htl-leo-club-embedded-iot/GoalFinder/docs/images/fotodoc_assemby/orig/PXL_20251103_104743675.jpg

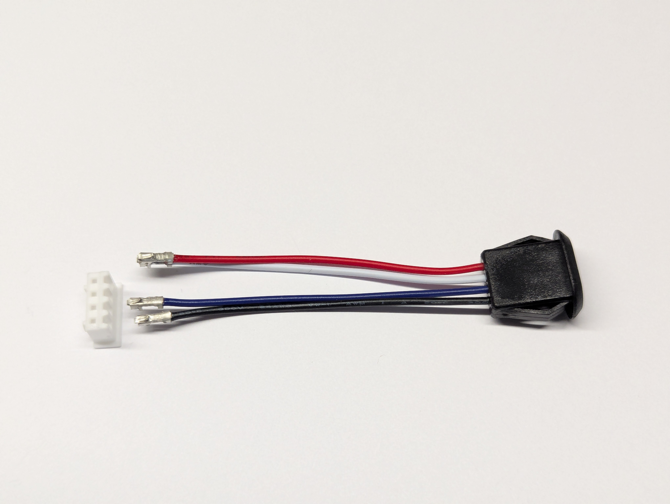
docs/images/fotodoc_assemby/orig/PXL_20251103_104743675.jpg
