htl-leo-club-embedded-iot/GoalFinder/docs/images/fotodoc_assemby/orig/PXL_20251103_160812800.jpg

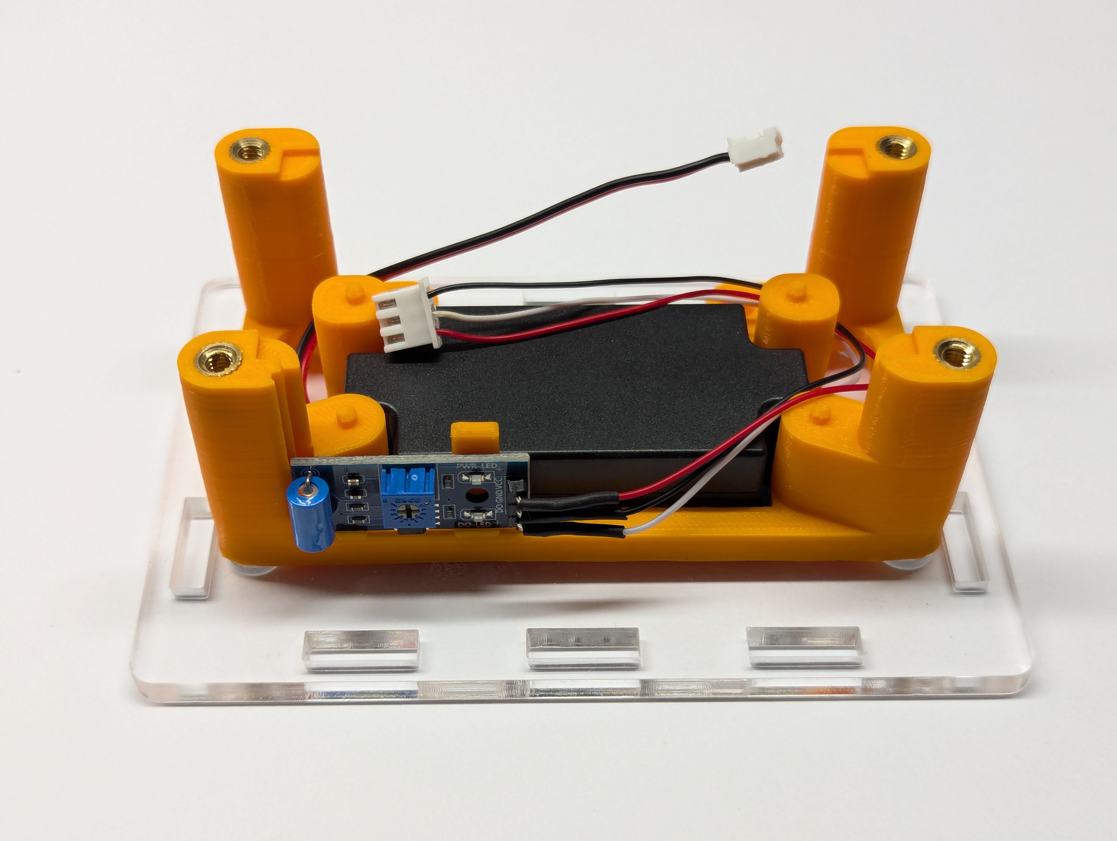
docs/images/fotodoc_assemby/orig/PXL_20251103_160812800.jpg
