htl-leo-club-embedded-iot/GoalFinder/docs/images/fotodoc_assemby/orig/PXL_20251103_201643062.jpg

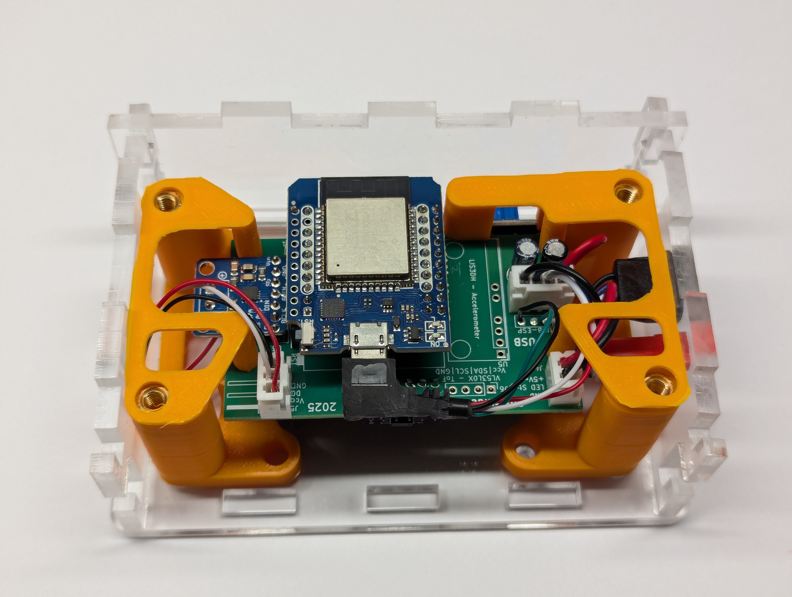
docs/images/fotodoc_assemby/orig/PXL_20251103_201643062.jpg
