htl-leo-club-embedded-iot/GoalFinder/docs/images/fotodoc_assemby/orig/PXL_20251103_222439220.jpg

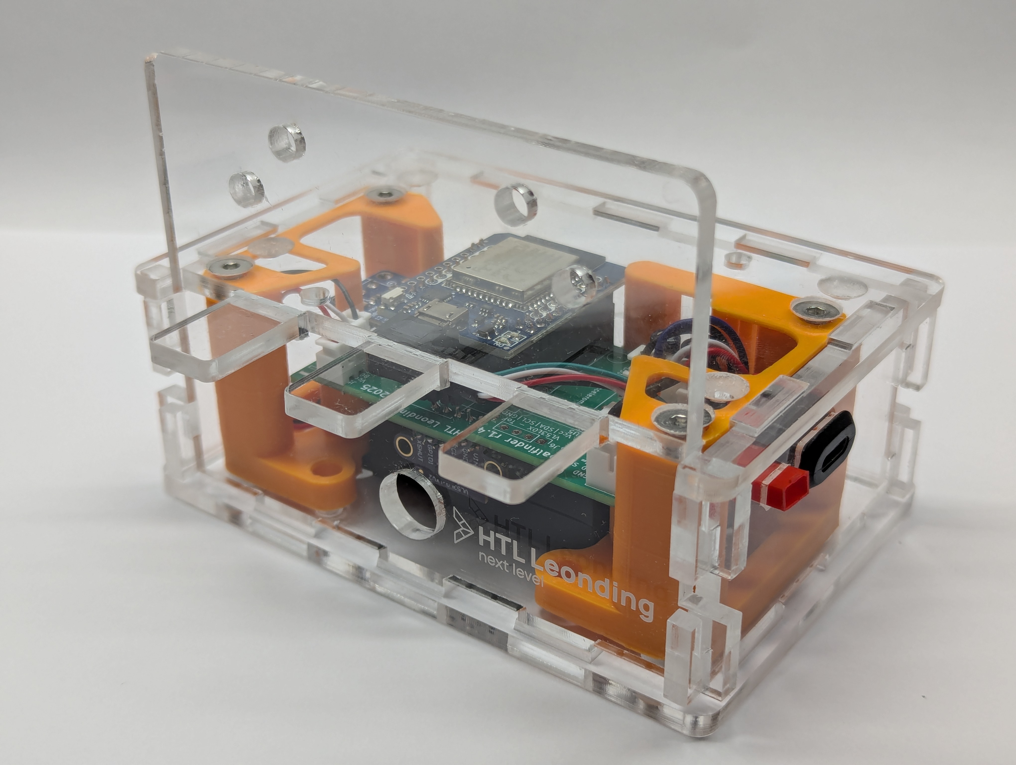
docs/images/fotodoc_assemby/orig/PXL_20251103_222439220.jpg
