htl-leo-club-embedded-iot/GoalFinder/embedded/src/util/Logger.h

/* ===============================================================================
 * (c) HTBLA Leonding 2024 - 2026
 * - - - - - - - - - - - - - - - - - - - - - - - - - - - - - - - - - - - - - - - -
 * Licensed under MIT License.
 *
 * Unless required by applicable law or agreed to in writing, software
 * distributed under the License is distributed on an "AS IS" BASIS,
 * WITHOUT WARRANTIES OR CONDITIONS OF ANY KIND, either express or implied.
 * See the License for the specific language governing permissions and
 * limitations under the license.
 * - - - - - - - - - - - - - - - - - - - - - - - - - - - - - - - - - - - - - - - -
 * All trademarks used in this document are property of their respective owners.
 * =============================================================================== */

#ifndef ___LOGGER_H
#define ___LOGGER_H

#include <WString.h>
#include "freertos/FreeRTOS.h"
#include "freertos/queue.h"
#include <Arduino.h>
#include "../Settings.h"

class Logger
{
public:
    enum class LogLevel
    {
        OK,
        DEBUG,
        INFO,
        WARN,
        ERROR
    };

    struct LogEntry {
        String message;
        String file;
        LogLevel level;
    };

    static void Begin(unsigned long baudRate = 115200);

    static void Log(const String &message);
    static void Log(const String &message, LogLevel level);
    static void Log(const String &message, const String &file, LogLevel level);
    static void LogExtra(const String &message, const String &file, LogLevel level);

    static void Log(const char *file, LogLevel level, const char *fmt, ...);
    static void LogExtra(const char *file, LogLevel level, const char *fmt, ...);

    static void Loop();
    static void DrainWebLogQueue();

private:
    static LogLevel currentLevel;
    static QueueHandle_t logQueue;
    static QueueHandle_t webLogQueue;

    static const char* LevelToString(LogLevel level);
    static void PrintNow(const LogEntry &entry);

    static void PrintFormatted(const String &message,
                               const String &file,
                               LogLevel level);

    static void Enqueue(const String &message,
                        const String &file,
                        LogLevel level);
};

#endif
